hyano/rp27c512/firmware/readline.h

/*
 * Copyright (c) 2024 Hirokuni Yano
 *
 * Released under the MIT license.
 * see https://opensource.org/licenses/MIT
 */
#ifndef READLINE_H__
#define READLINE_H__

#include <stdint.h>

void readline(char *buffer, int32_t size);

#endif
