hyano/rp27c512/firmware/microrl_user_config.h

/*
 * Copyright (c) 2024 Hirokuni Yano
 *
 * Released under the MIT license.
 * see https://opensource.org/licenses/MIT
 */
#ifndef MICRORL_USER_CONFIG_H__
#define MICRORL_USER_CONFIG_H__

#ifdef __cplusplus
extern "C" {
#endif /* __cplusplus */

#define MICRORL_CFG_USE_COMPLETE              1
#define MICRORL_CFG_USE_HISTORY               1
#define MICRORL_CFG_END_LINE                  "\n"

#ifdef __cplusplus
}
#endif /* __cplusplus */

#endif  /* MICRORL_USER_CONFIG_H__ */
